xxpasixx/EvoFaderWing/docs/images/evofaderwing_keyboard_matrix_wring.png

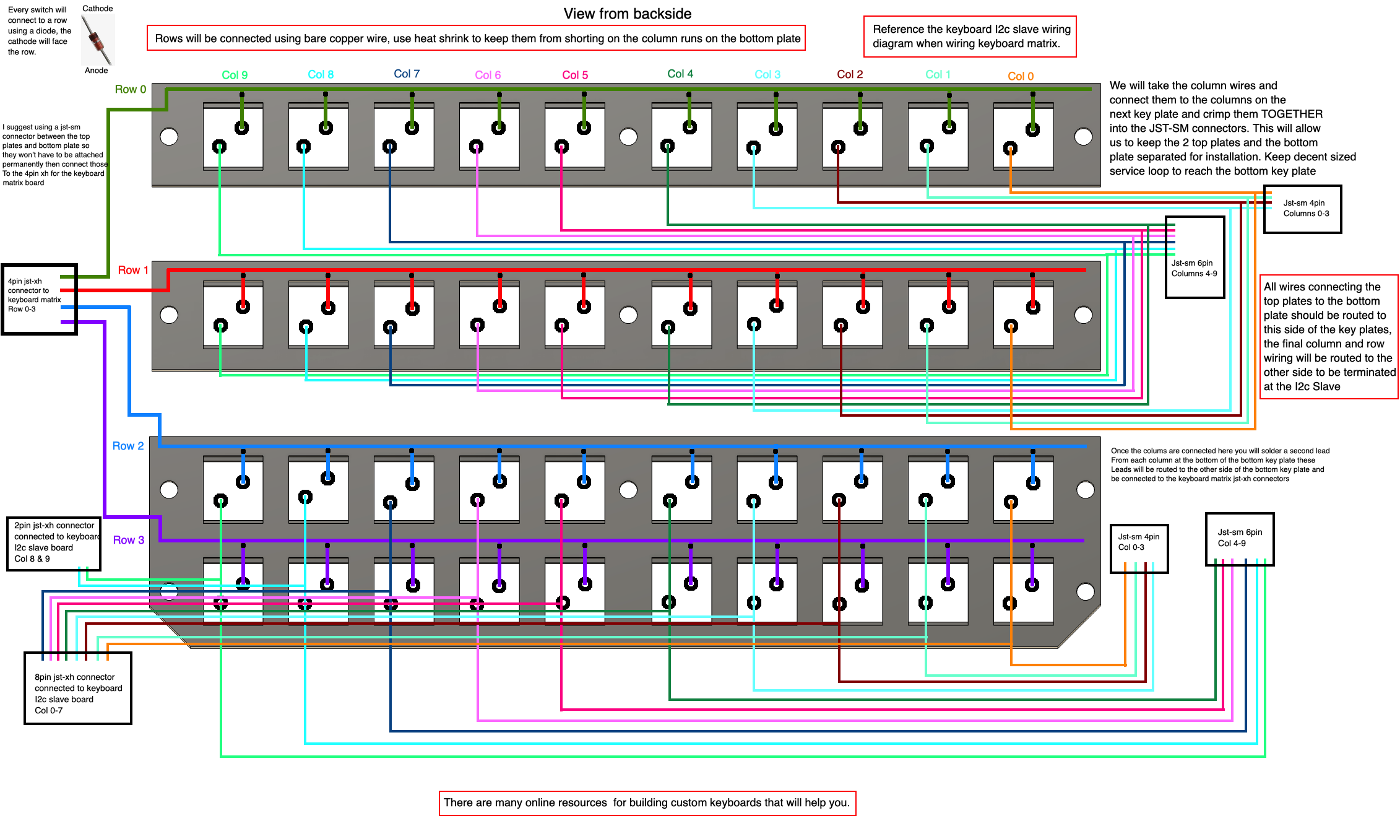
docs/images/evofaderwing_keyboard_matrix_wring.png
