xxpasixx/EvoFaderWing/docs/images/fader_images/fader_power_rail.jpeg

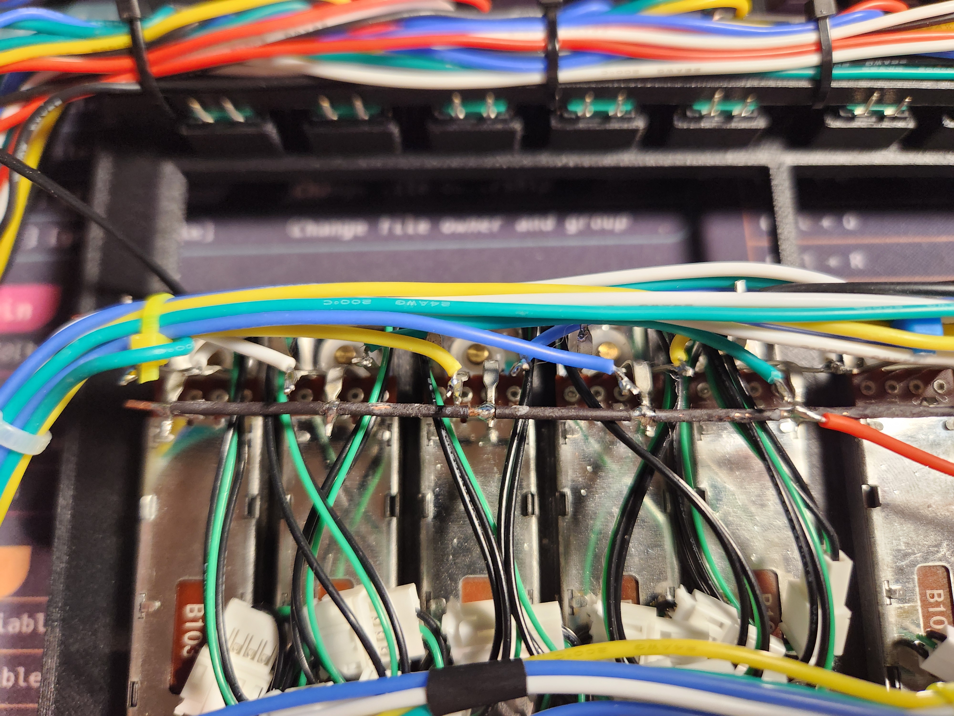
docs/images/fader_images/fader_power_rail.jpeg
