xxpasixx/EvoFaderWing/docs/images/keyplate_images/key_plates_top_middle.jpeg

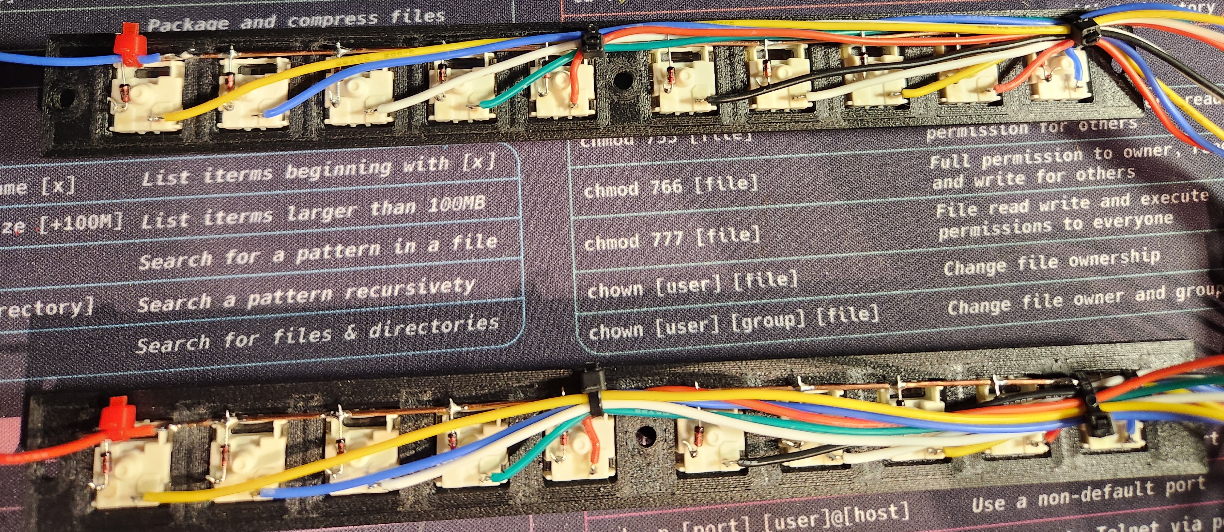
docs/images/keyplate_images/key_plates_top_middle.jpeg
