xxpasixx/EvoFaderWing/docs/images/led_images/led_connectors_tuckedin.jpg

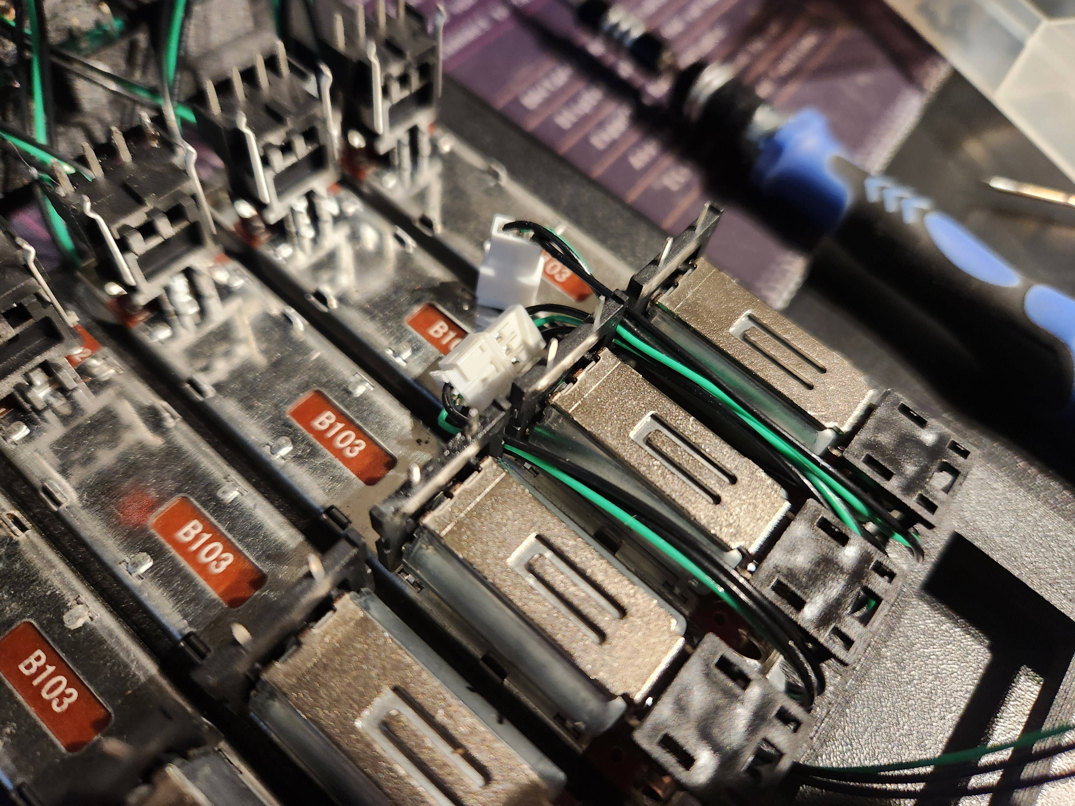
docs/images/led_images/led_connectors_tuckedin.jpg
