xxpasixx/EvoFaderWing/docs/images/led_images/led_strip_placed.jpg

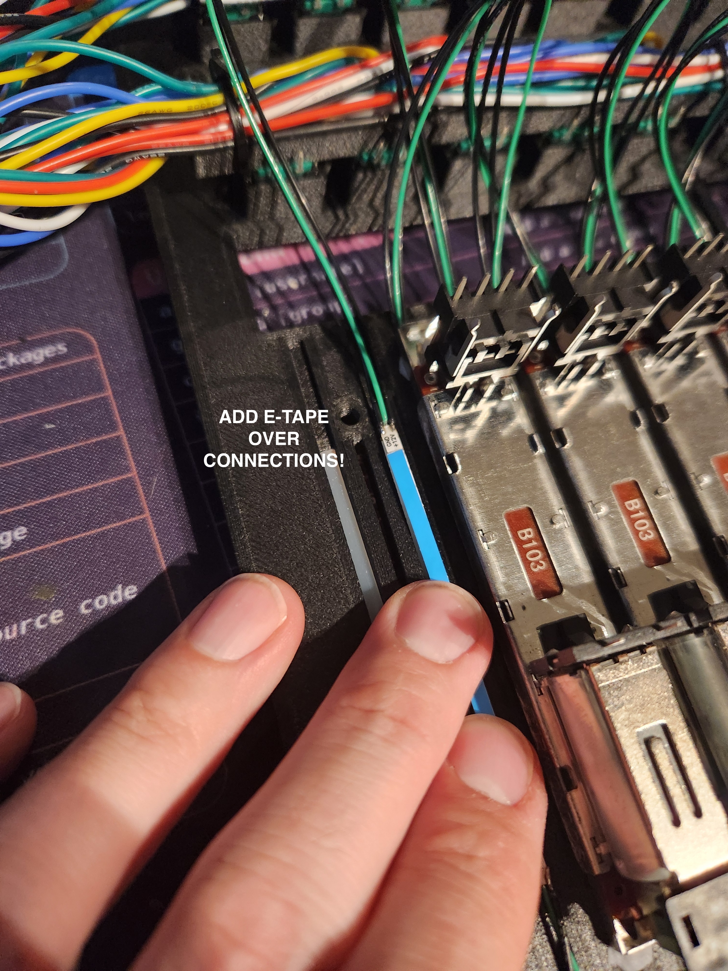
docs/images/led_images/led_strip_placed.jpg
