xxpasixx/EvoFaderWing/docs/images/misc/20250524_153631.jpg

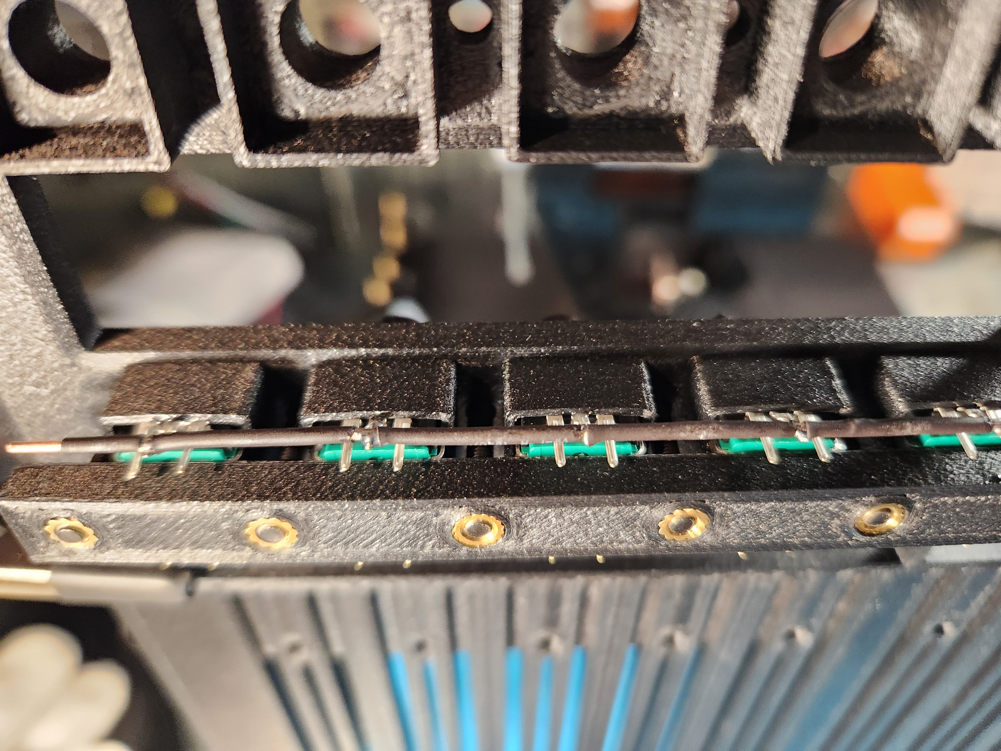
docs/images/misc/20250524_153631.jpg
