xxpasixx/EvoFaderWing/docs/images/misc/20250524_165157.jpg

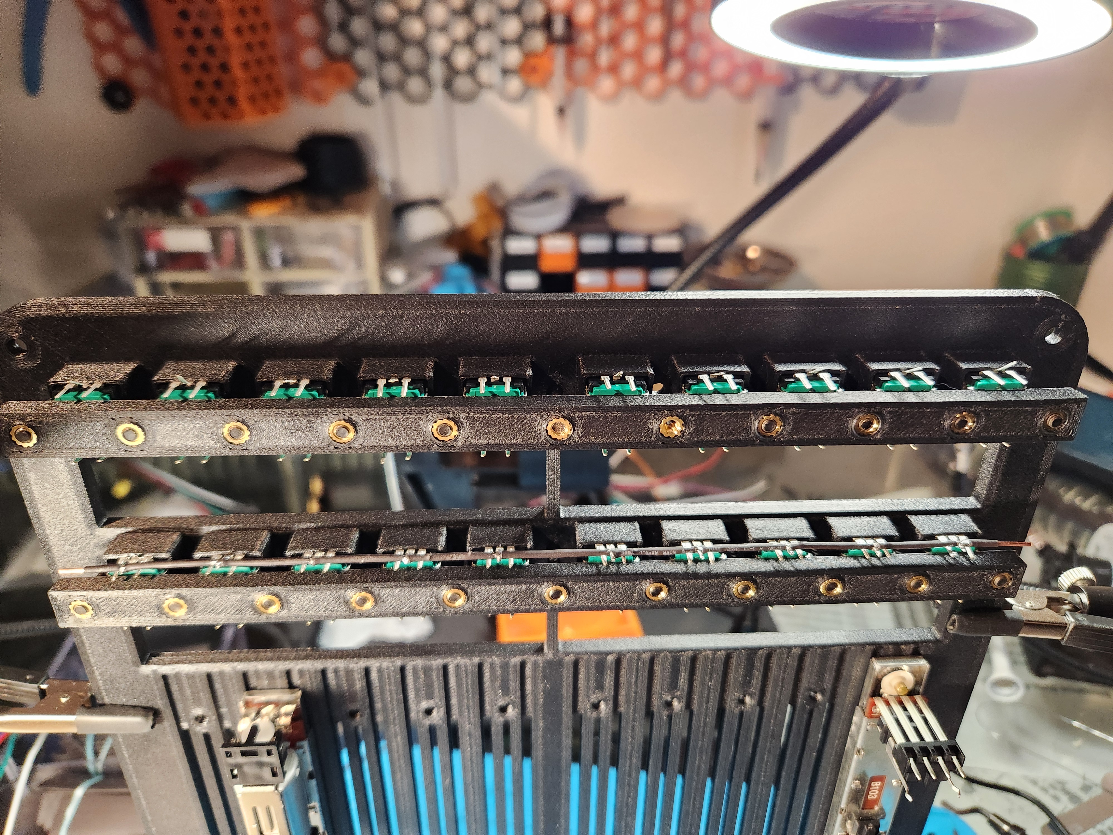
docs/images/misc/20250524_165157.jpg
