xxpasixx/EvoFaderWing/docs/images/misc/20250524_171109.jpg

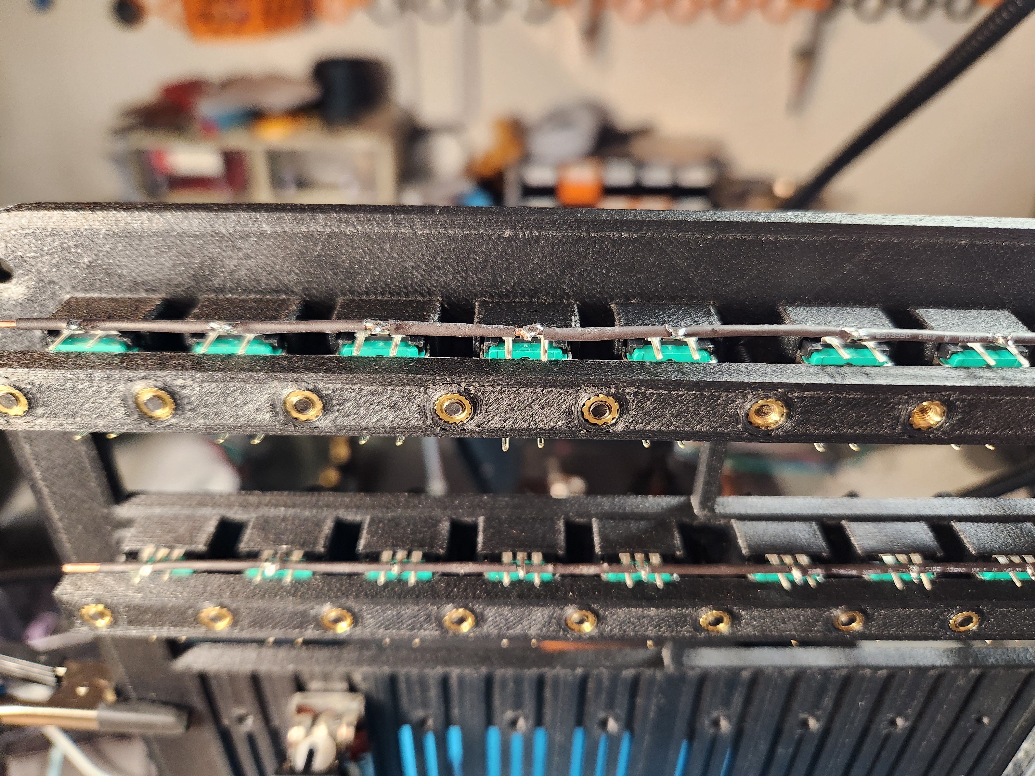
docs/images/misc/20250524_171109.jpg
