xxpasixx/EvoFaderWing/docs/images/misc/20250525_133858.jpg

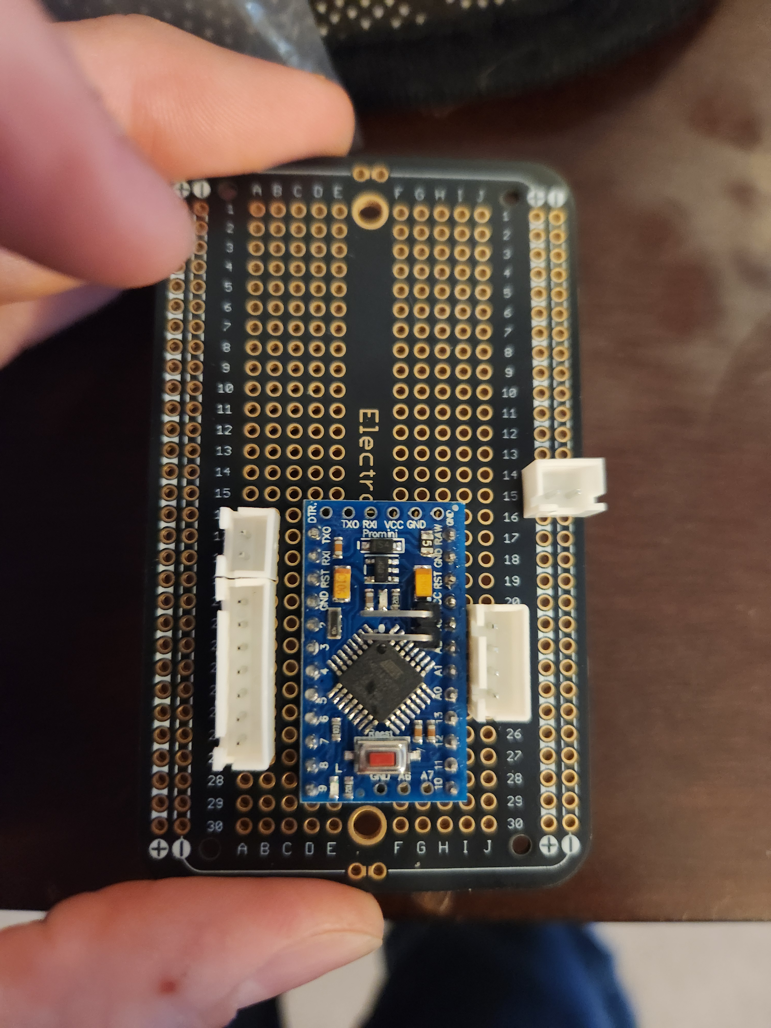
docs/images/misc/20250525_133858.jpg
