xxpasixx/EvoFaderWing/docs/images/misc/20250607_174612.jpg

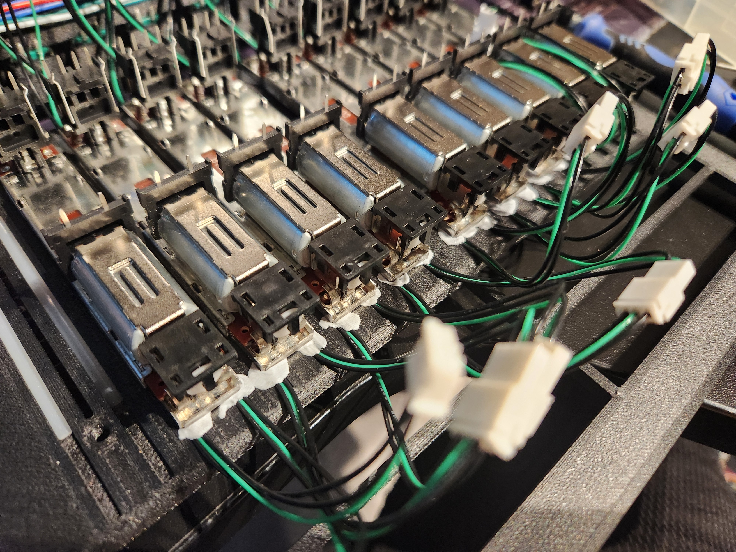
docs/images/misc/20250607_174612.jpg
