xxpasixx/EvoFaderWing/docs/images/misc/20250607_201828.jpg

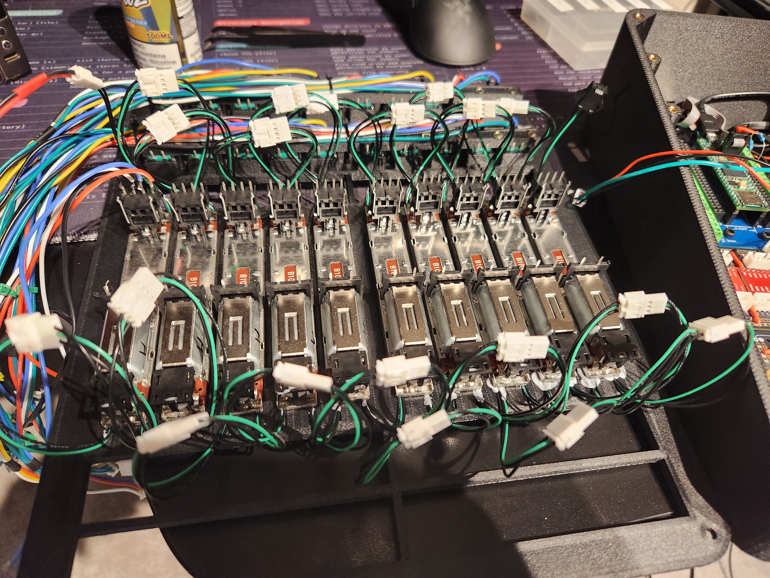
docs/images/misc/20250607_201828.jpg
