xxpasixx/EvoFaderWing/docs/images/misc/20250608_192833.jpg

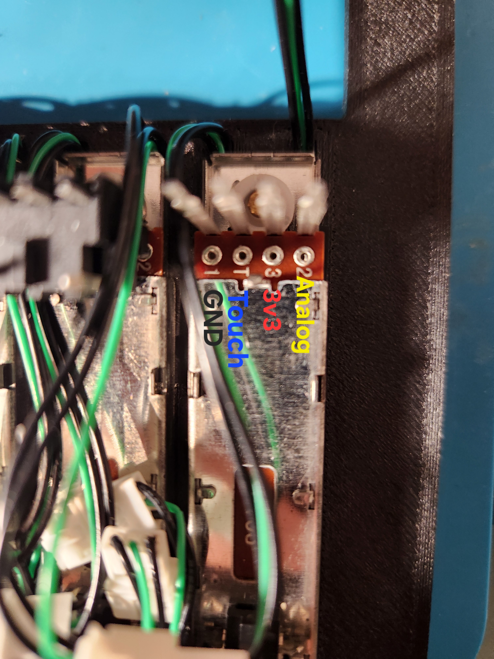
docs/images/misc/20250608_192833.jpg
