xxpasixx/EvoFaderWing/docs/images/misc/20250608_230007.jpg

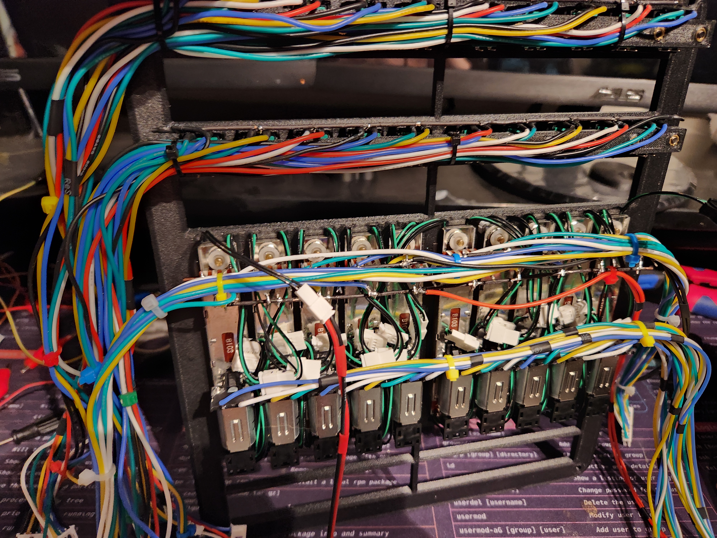
docs/images/misc/20250608_230007.jpg
