xxpasixx/EvoFaderWing/docs/images/misc/20250608_230014.jpg

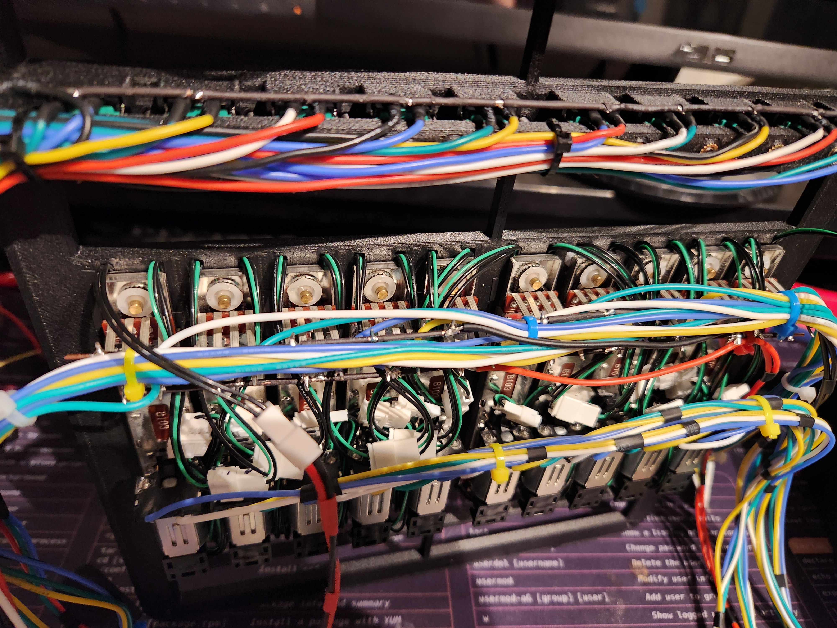
docs/images/misc/20250608_230014.jpg
