xxpasixx/EvoFaderWing/docs/images/misc/20250608_230018.jpg

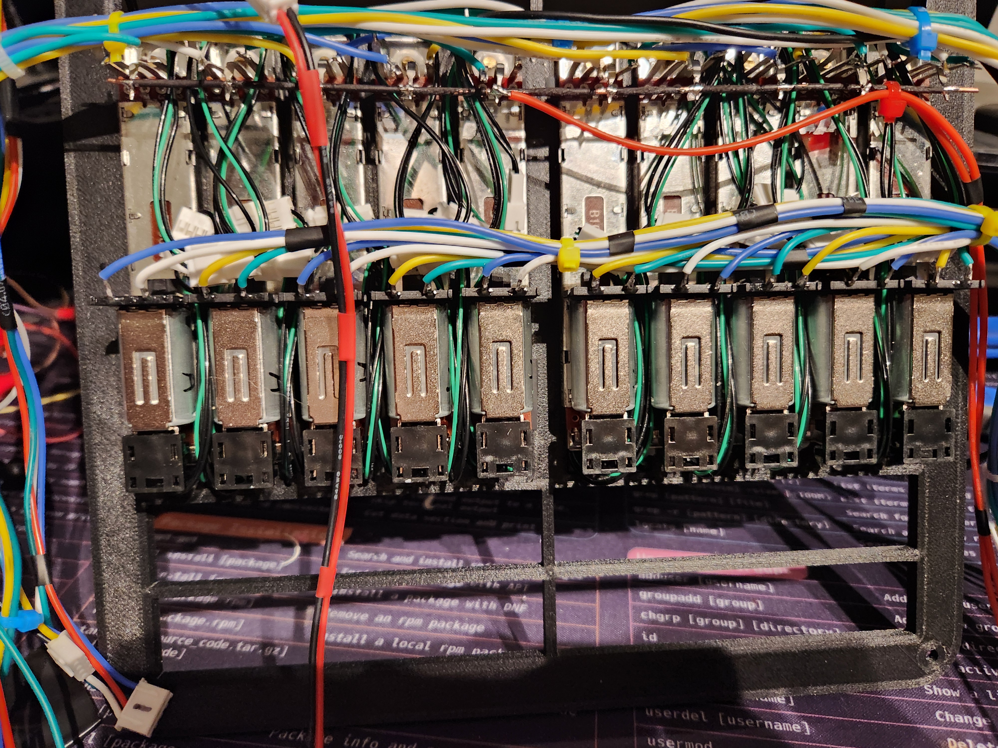
docs/images/misc/20250608_230018.jpg
