xxpasixx/EvoFaderWing/docs/images/misc/20250608_230021.jpg

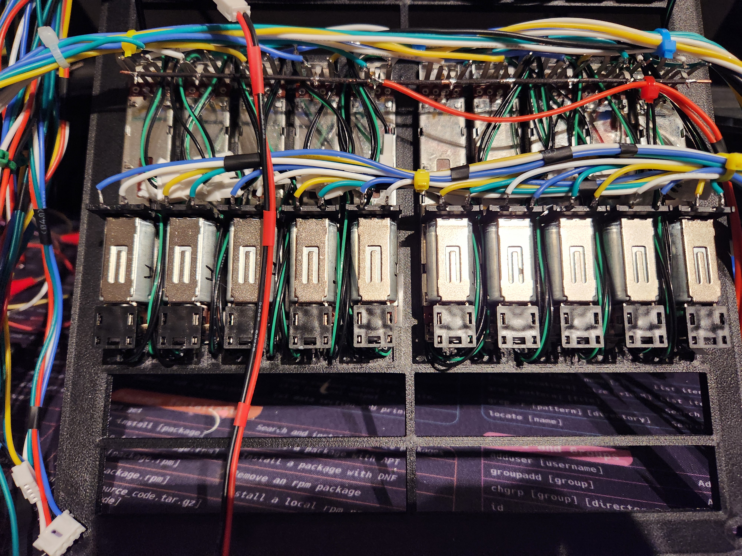
docs/images/misc/20250608_230021.jpg
