xxpasixx/EvoFaderWing/docs/images/misc/20250609_000330.jpg

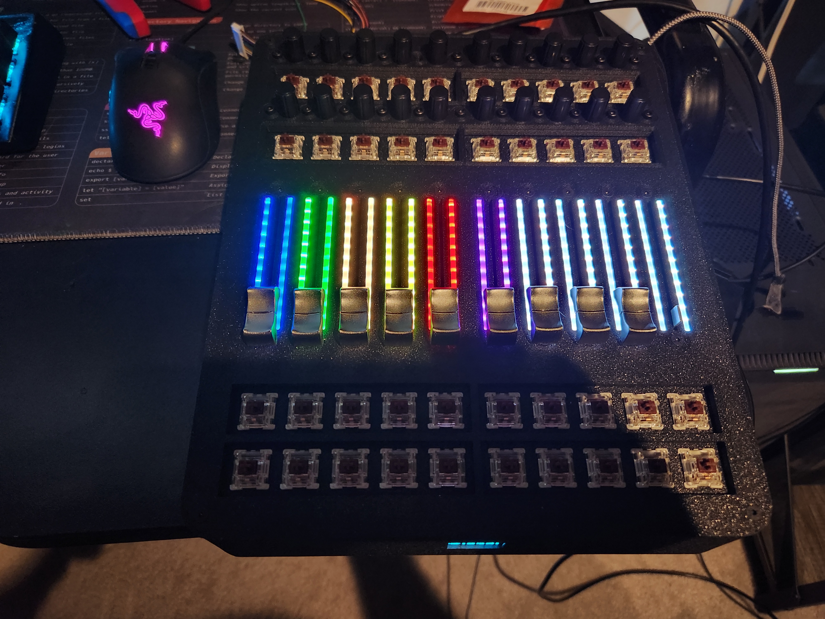
docs/images/misc/20250609_000330.jpg
