xxpasixx/EvoFaderWing/docs/images/misc/20250616_111618.jpg

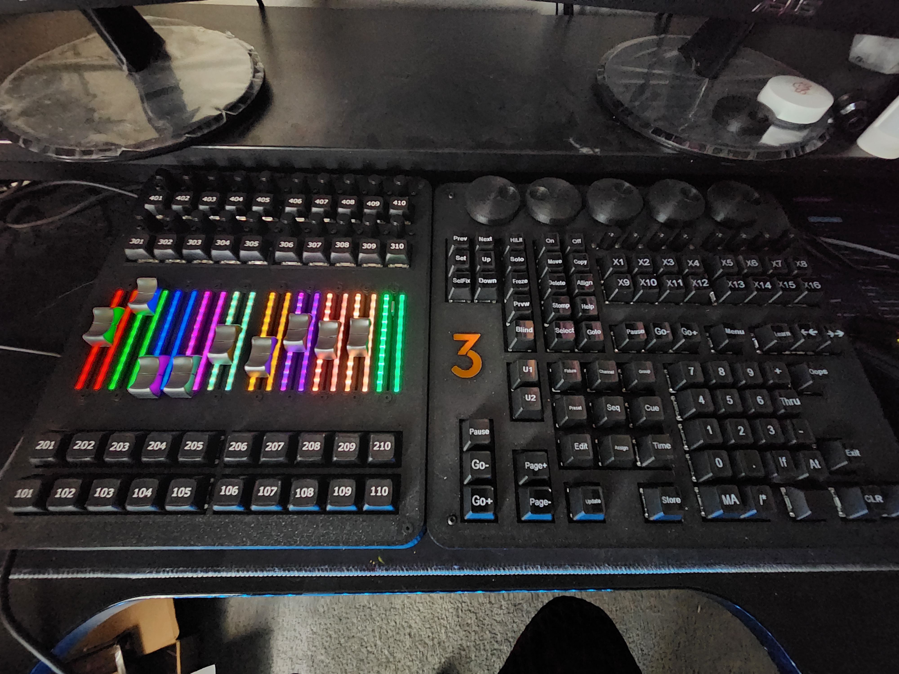
docs/images/misc/20250616_111618.jpg
