xxpasixx/EvoFaderWing/docs/images/pin_assignment.png

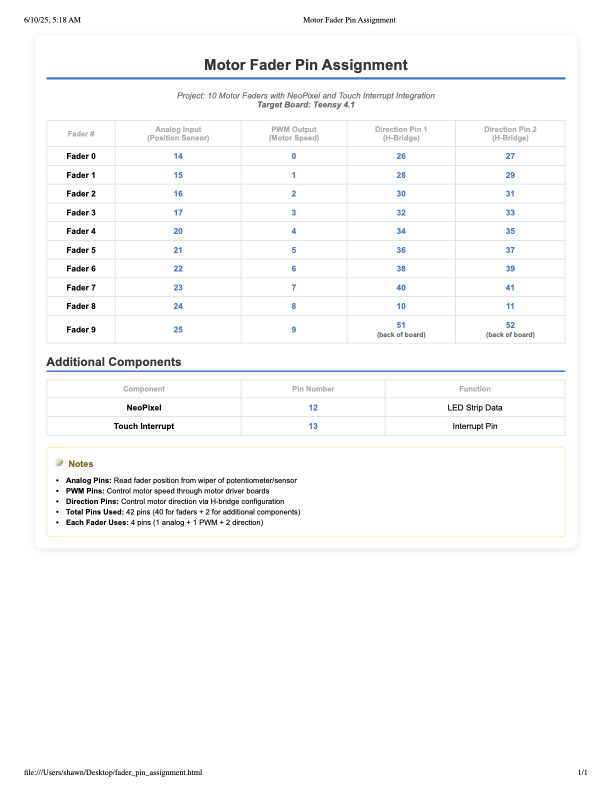
docs/images/pin_assignment.png
