xxpasixx/EvoFaderWing/docs/images/assembly/assembly_7.jpg

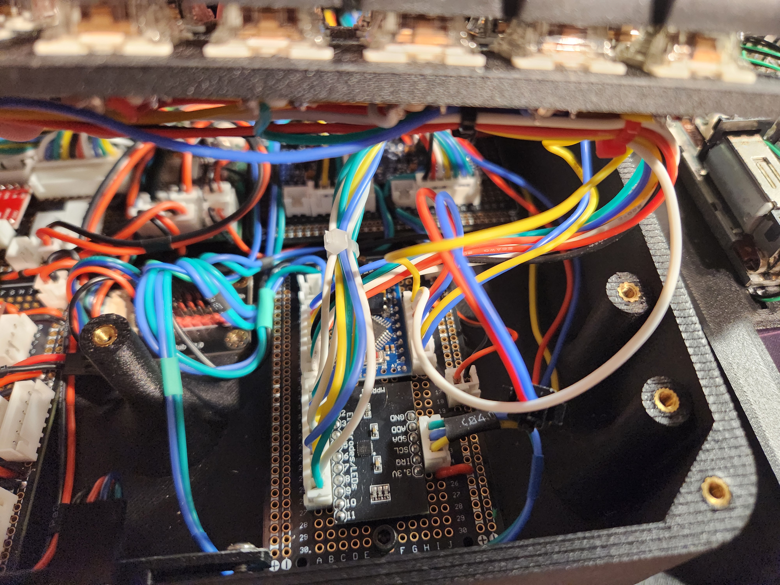
docs/images/assembly/assembly_7.jpg
