xxpasixx/EvoFaderWing/docs/images/assembly/assembly_9.jpg

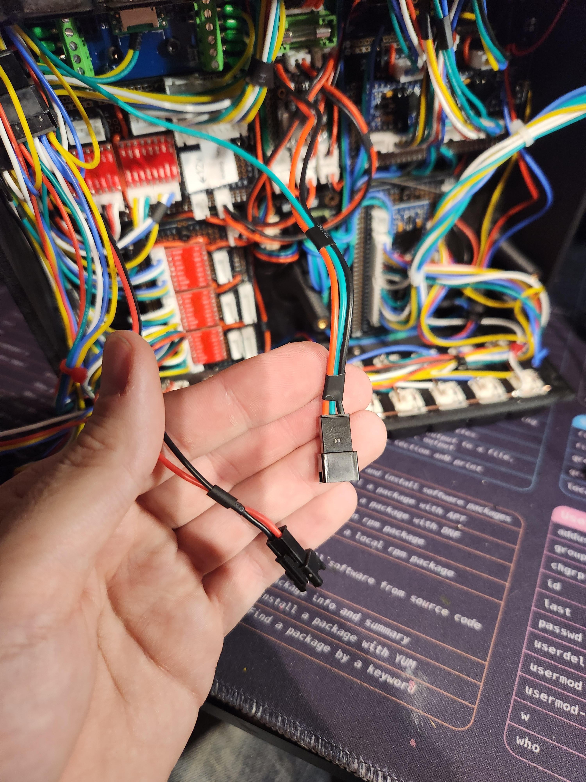
docs/images/assembly/assembly_9.jpg
