xxpasixx/EvoFaderWing/docs/images/assembly/assembly_10.jpg

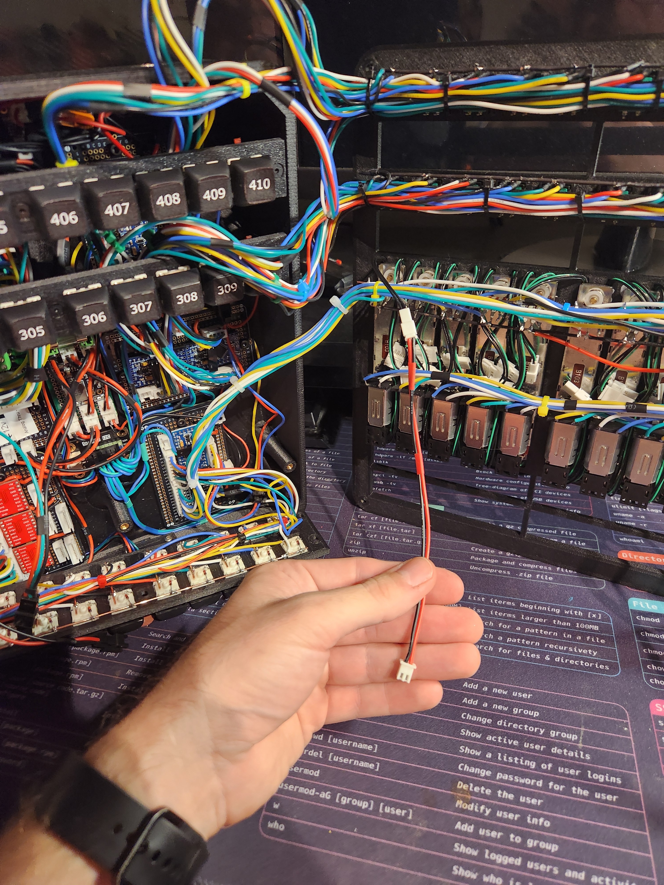
docs/images/assembly/assembly_10.jpg
