xxpasixx/EvoFaderWing/docs/images/assembly/assembly_14.jpg

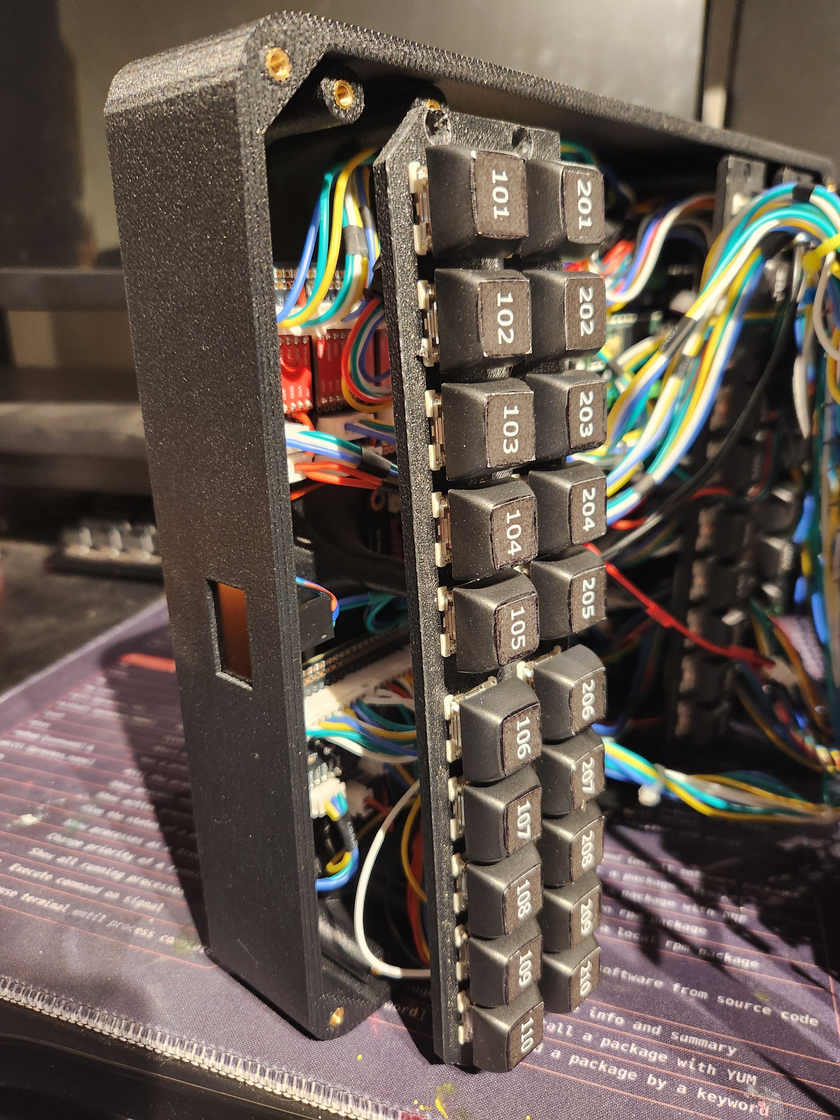
docs/images/assembly/assembly_14.jpg
