xxpasixx/EvoFaderWing/docs/images/evofaderwing_encoder_slave_wiring.png

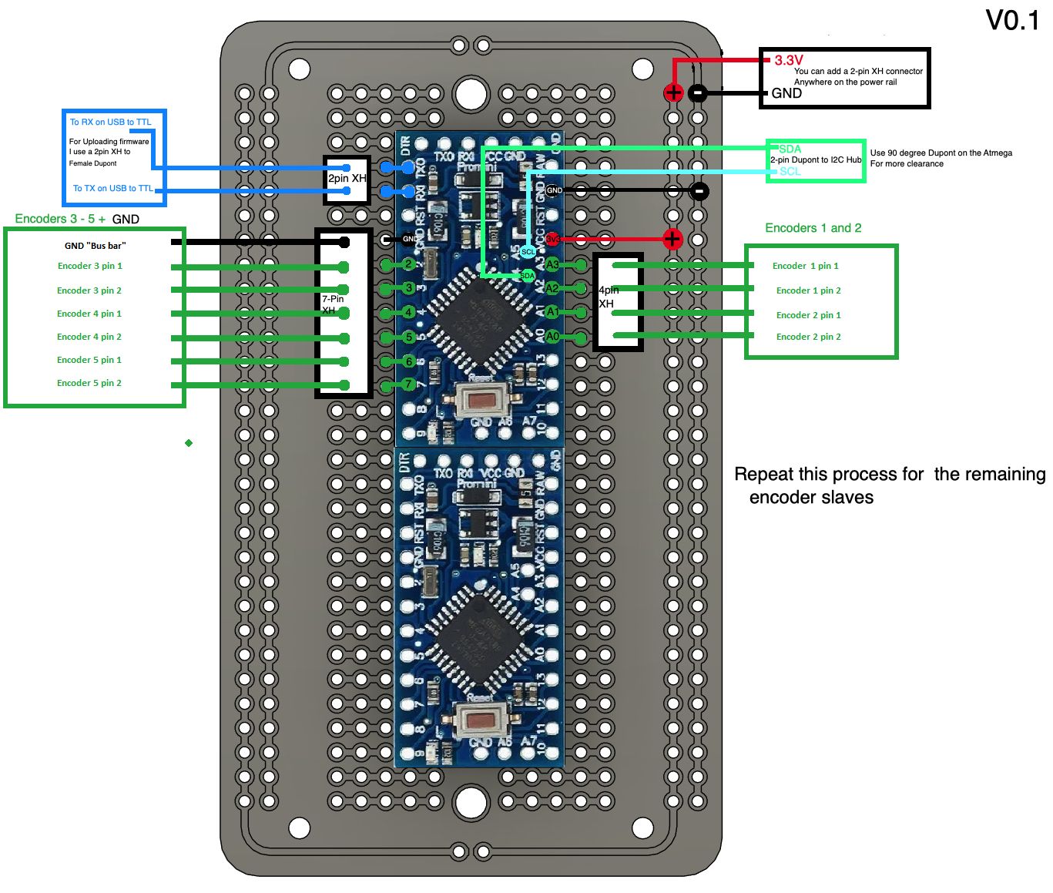
docs/images/evofaderwing_encoder_slave_wiring.png
