xxpasixx/EvoFaderWing/docs/images/evofaderwing_motor_wiring.png

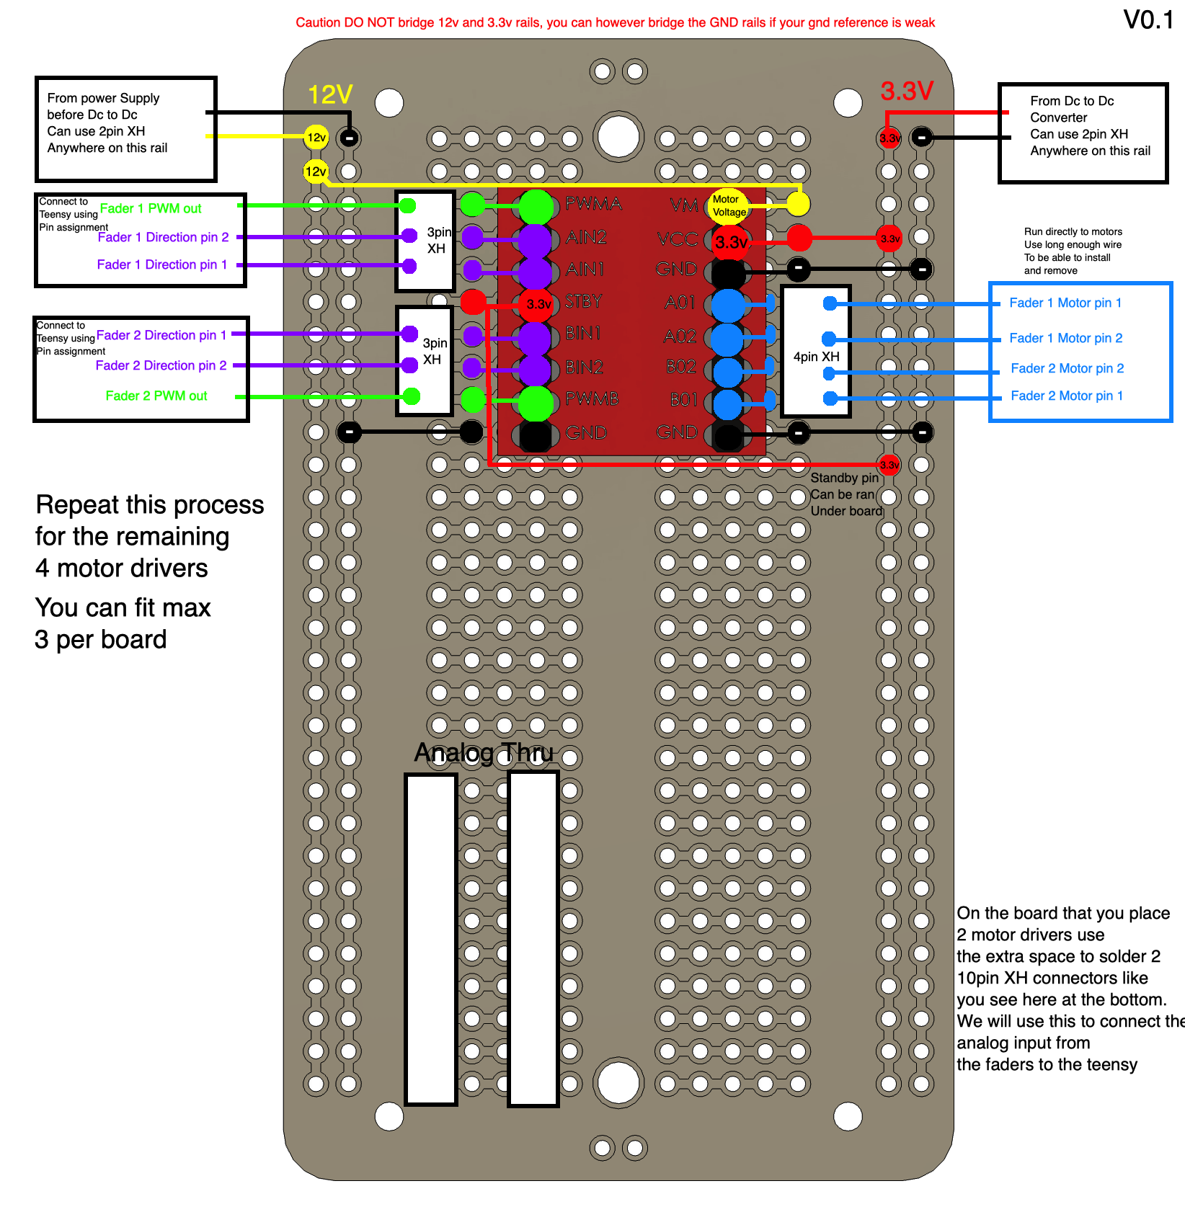
docs/images/evofaderwing_motor_wiring.png
