xxpasixx/EvoFaderWing/src/Config.cpp

// Config.cpp
#include "Config.h"

//================================
// MAIN FADER ARRAY
//================================
// Holds runtime data for each motorized fader.
// This is the primary data structure manipulated by control logic.
Fader faders[NUM_FADERS];

//================================
// PIN CONFIGURATION ARRAYS
//================================
// Analog input pins connected to fader position sensors (wipers).
const uint8_t ANALOG_PINS[NUM_FADERS] = {14, 15, 16, 17, 20, 21, 22, 23, 24, 25};

// PWM output pins used to control fader motor speed via motor drivers.
const uint8_t PWM_PINS[NUM_FADERS] = {0, 1, 2, 3, 4, 5, 6, 7, 8, 9};

//USE 12 for NEOPIXEL
//USE 41 for MRP121/MTCH2120 IRQ
//USE 18 (SDA), 19(SCL) for I2C

// Motor direction control pins — each fader has two pins for H-bridge control.
const uint8_t DIR_PINS1[NUM_FADERS] = {26, 28, 30, 32, 34, 36, 38, 40, 10, 51};
const uint8_t DIR_PINS2[NUM_FADERS] = {27, 29, 31, 33, 35, 37, 39, 41, 11, 52};

// Unique OSC IDs for each fader (used to construct OSC address strings).
const uint16_t OSC_IDS[NUM_FADERS] = {201, 202, 203, 204, 205, 206, 207, 208, 209, 210};

//================================
// FADER BEHAVIOR CONFIGURATION
//================================
// Default PID and motor tuning settings shared across all faders.
FaderConfig Fconfig = {
  .minPwm = MIN_PWM,
  .maxPwm = MAX_PWM,
  .calibratePwm = CALIB_PWM,
  .targetTolerance = TARGET_TOLERANCE,
  .sendTolerance = SEND_TOLERANCE,
  .slowZone = SLOW_ZONE,
  .fastZone = FAST_ZONE,
  .baseBrightness = 5,
  .touchedBrightness = 40,
  .fadeTime = 500,
  .serialDebug = debugMode,
  .sendKeystrokes = false,
  .useLevelPixels = false

};

// Executor LED defaults
ExecConfig execConfig = {
  .baseBrightness = EXECUTOR_BASE_BRIGHTNESS,
  .activeBrightness = EXECUTOR_ACTIVE_BRIGHTNESS,
  .useStaticColor = false,
  .staticRed = 255,
  .staticGreen = 255,
  .staticBlue = 255,
  .reserved = {0, 0}
};

//================================
// NETWORK CONFIGURATION
//================================
// Default static network settings and UDP destination info.
// These values can be updated at runtime or overridden via web UI.
NetworkConfig netConfig = {
  IPAddress(192, 168, 0, 169),     // staticIP
  IPAddress(192, 168, 0, 1),       // gateway
  IPAddress(255, 255, 255, 0),     // subnet
  IPAddress(192, 168, 0, 10),     // sendToIP (OSC target)
  8000,                            // receivePort (OSC listening)
  9000,                            // sendPort (OSC destination)
  true                             // useDHCP (fallback to static if false)
};

// Network reset check
bool checkForReset = true;
unsigned long resetCheckStartTime = 0;

// Calibration state flag
bool calibrationInProgress = false;


//================================
// DEBUG SETTINGS
//================================
#ifdef DEBUG
  bool debugMode = true;  // Enables or disables verbose serial output
#else
  bool debugMode = false;  // Enables or disables verbose serial output
#endif

//================================
// TOUCH SENSOR GLOBALS
//================================
// These are used by the touch driver and web UI configuration.
int autoCalibrationMode = 1;      // 0 = AutoTune off, 1 = AutoTune on
#if defined(TOUCH_SENSOR_MTCH2120)
uint8_t touchThreshold = 128;     // Higher = less sensitive (MTCH2120 per-key threshold)
uint8_t releaseThreshold = 1;     // Hysteresis code 0-7
#else
uint8_t touchThreshold = 12;      // Higher = less sensitive (MPR121 default)
uint8_t releaseThreshold = 6;     // Lower = harder to release (MPR121 default)
#endif


// Page Tracking
int currentOSCPage = 1;  // Default to page 1
