xxpasixx/EvoFaderWing/include/Utils.h

// Utils.h
#ifndef UTILS_H
#define UTILS_H

#include <Arduino.h>
#include <IPAddress.h>

//================================
// DEBUG FUNCTIONS
//================================

// Debug print functions - only output if debug mode is enabled
void debugPrint(const char* message);
void debugPrintf(const char* format, ...);


//================================
// UPLOAD FUNCTION
//================================
void checkSerialForReboot();   //Allow us to upload without pressing physical button
void processSerialCommand(String cmd);

//================================
// IP ADDRESS UTILITIES
//================================

// IP address conversion helpers
String ipToString(IPAddress ip);
IPAddress stringToIP(const String &str);

//================================
// WEB PARAMETER PARSING
//================================

// Extract parameter from URL query string
String getParam(String data, const char* key);

// Reset Teensy
void resetTeensy();

#endif // UTILS_H
