xxpasixx/EvoFaderWing/docs/images/led_images/led_strips.jpg

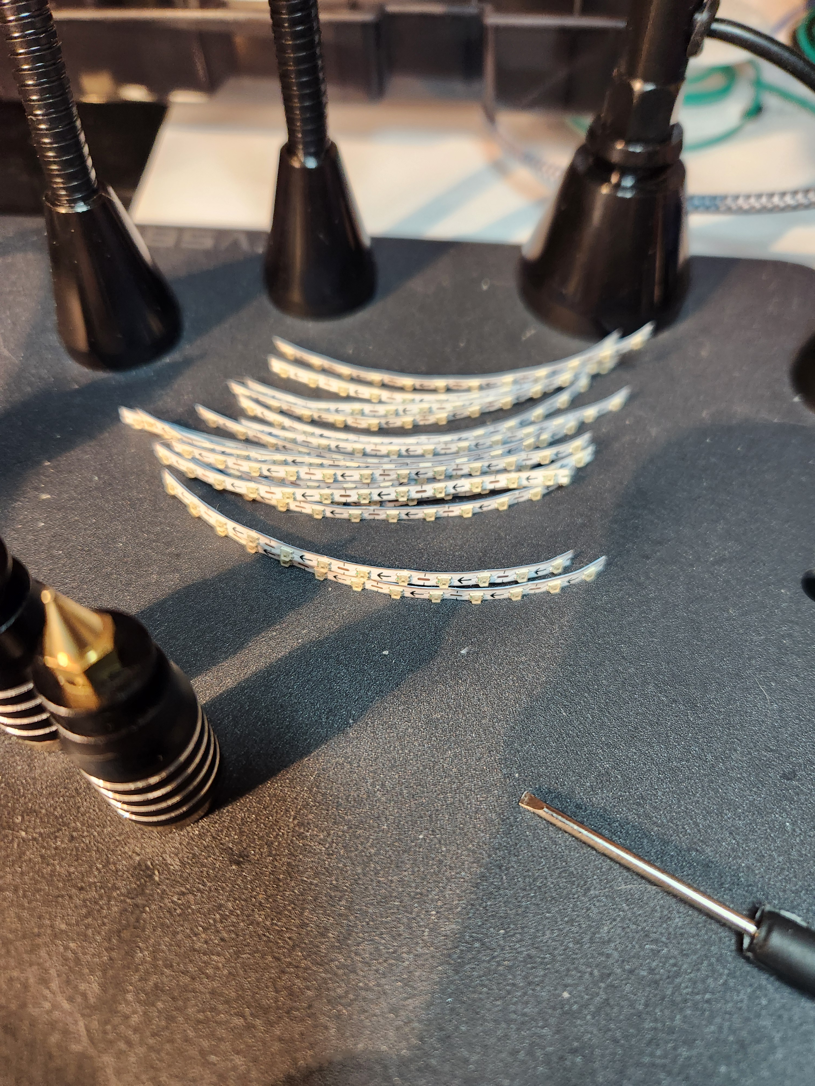
docs/images/led_images/led_strips.jpg
