xxpasixx/EvoFaderWing/docs/images/misc/20250525_185512.jpg

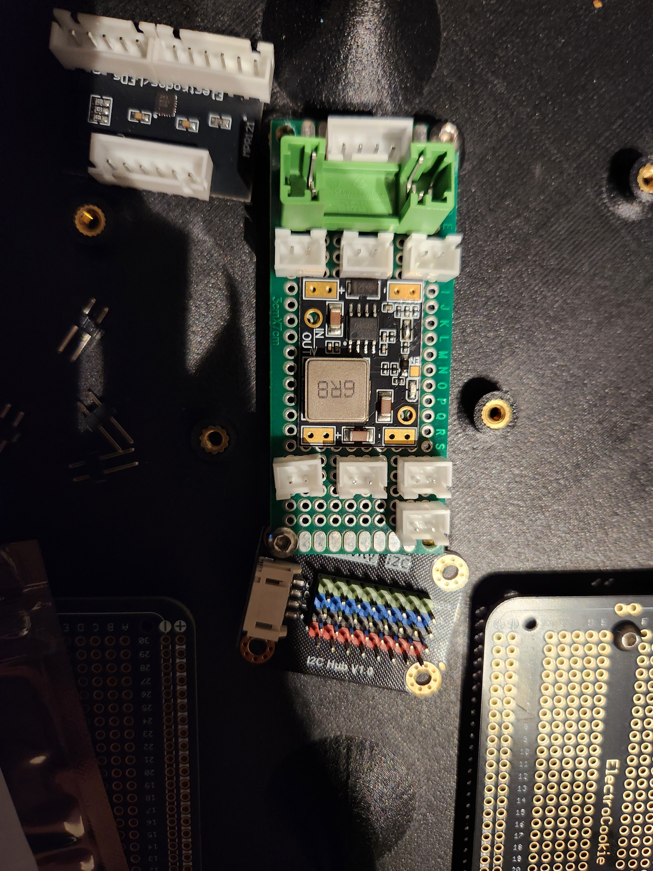
docs/images/misc/20250525_185512.jpg
