xxpasixx/EvoFaderWing/docs/images/misc/20250530_231826.jpg

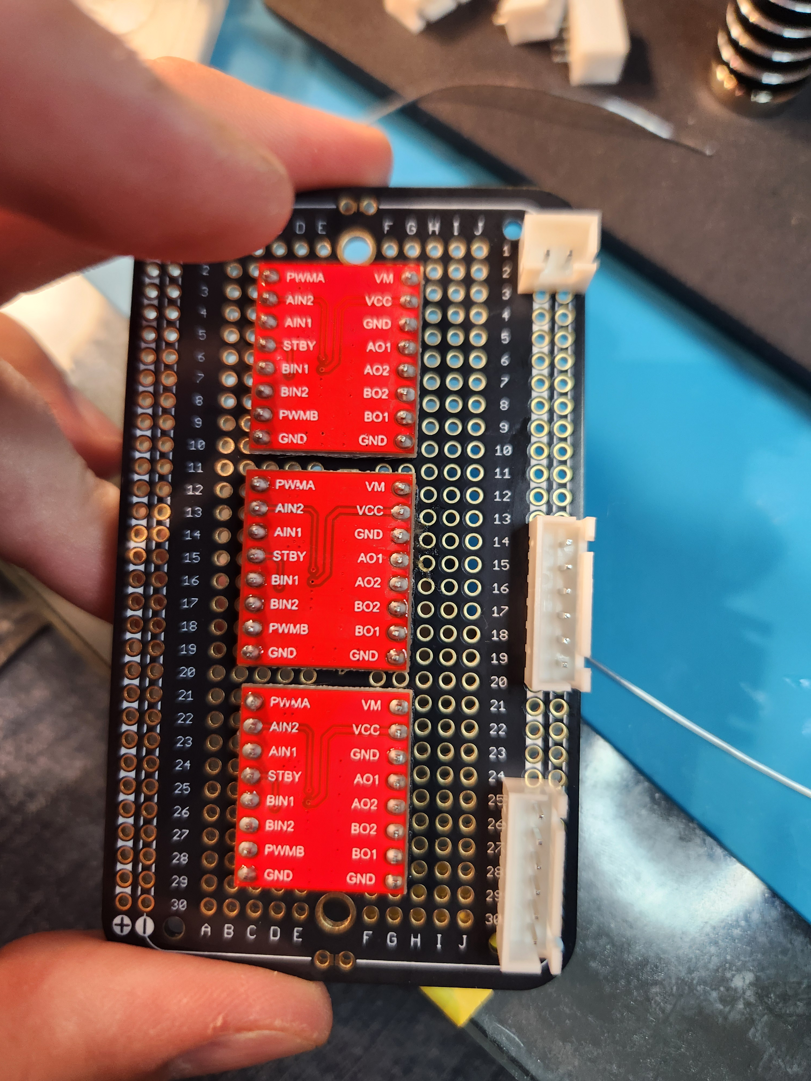
docs/images/misc/20250530_231826.jpg
