xxpasixx/EvoFaderWing/docs/images/misc/20250607_174801.jpg

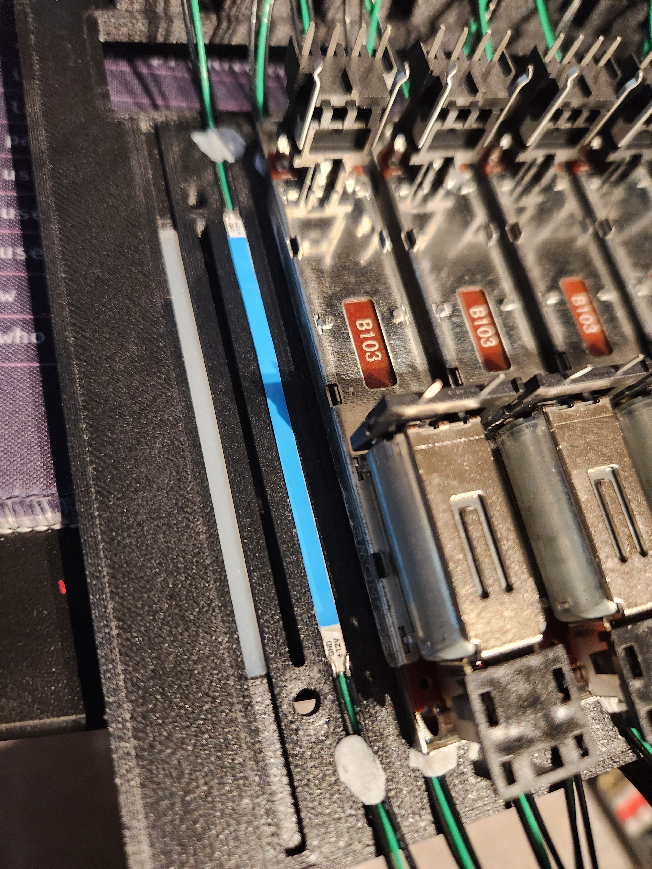
docs/images/misc/20250607_174801.jpg
