xxpasixx/EvoFaderWing/docs/images/misc/20250607_175227.jpg

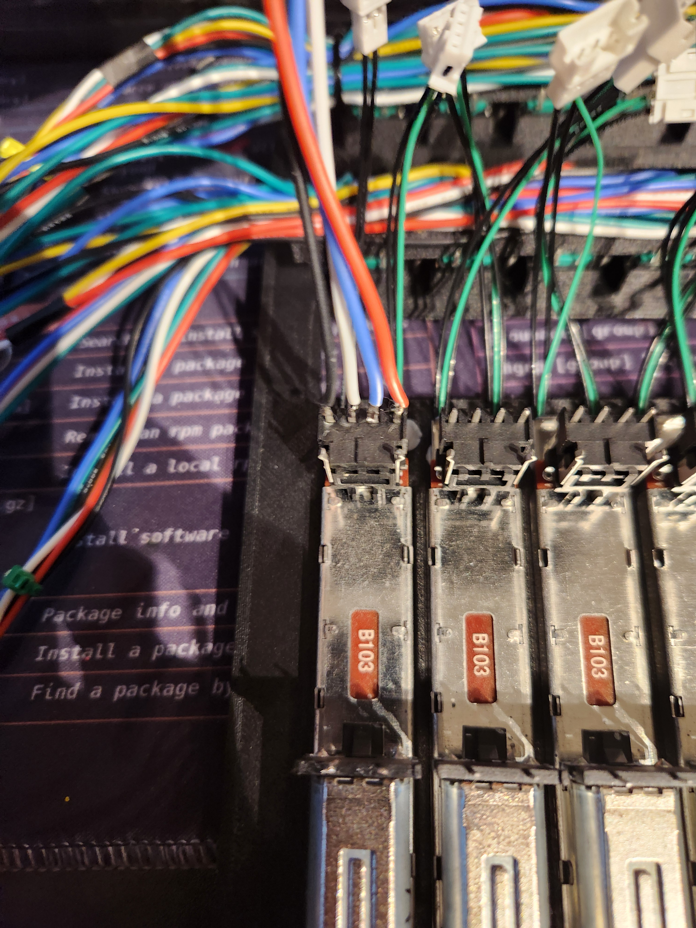
docs/images/misc/20250607_175227.jpg
