xxpasixx/EvoFaderWing/docs/images/misc/20250607_201822.jpg

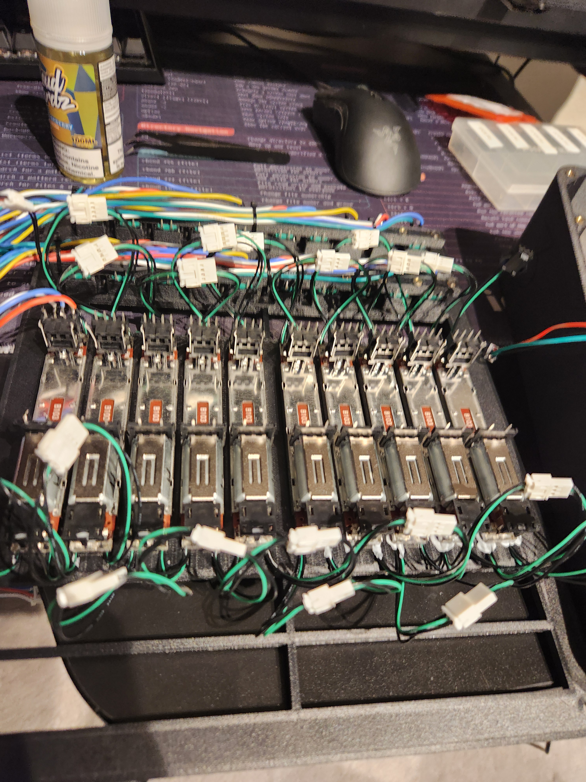
docs/images/misc/20250607_201822.jpg
