xxpasixx/EvoFaderWing/docs/images/misc/20250608_225934.jpg

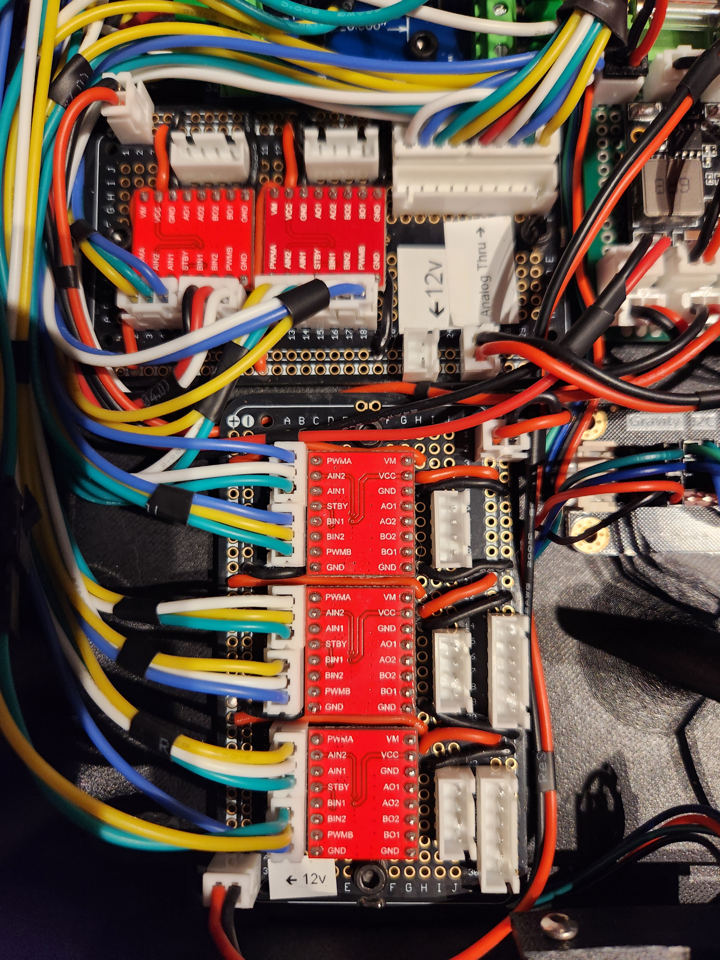
docs/images/misc/20250608_225934.jpg
