xxpasixx/EvoFaderWing/docs/images/misc/20250608_225937.jpg

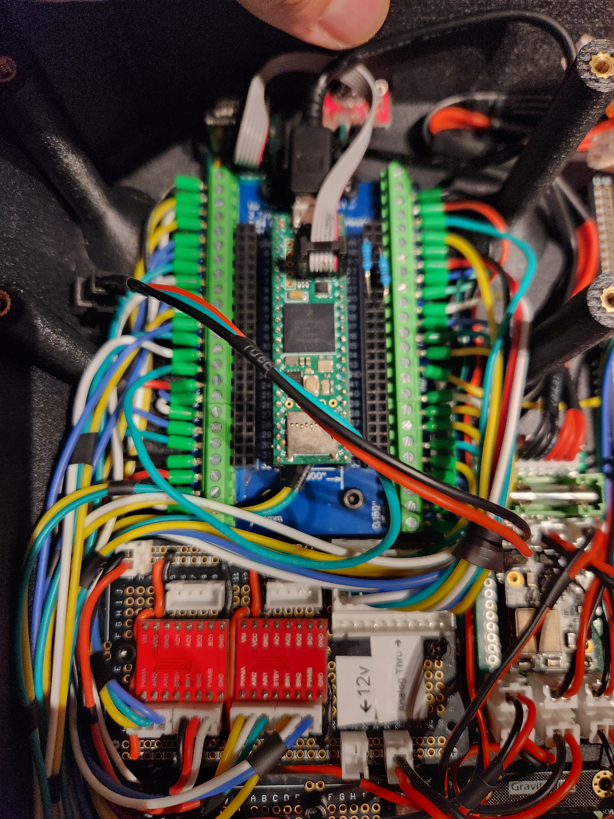
docs/images/misc/20250608_225937.jpg
