xxpasixx/EvoFaderWing/docs/images/misc/20250608_225939.jpg

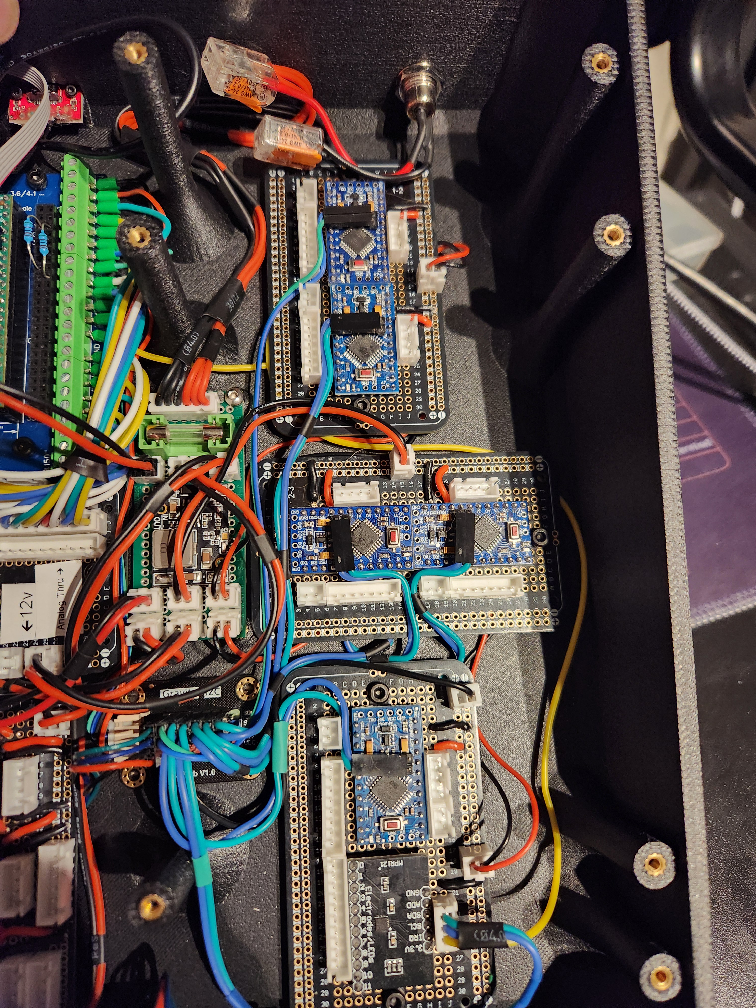
docs/images/misc/20250608_225939.jpg
