xxpasixx/EvoFaderWing/docs/images/misc/20250608_225953.jpg

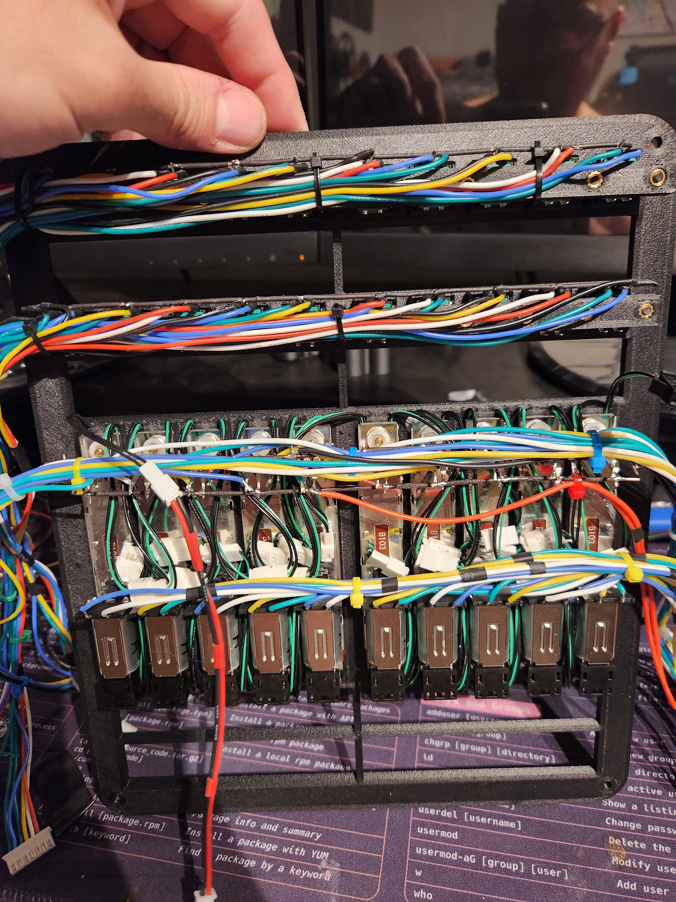
docs/images/misc/20250608_225953.jpg
