xxpasixx/EvoFaderWing/docs/images/misc/20250608_230002.jpg

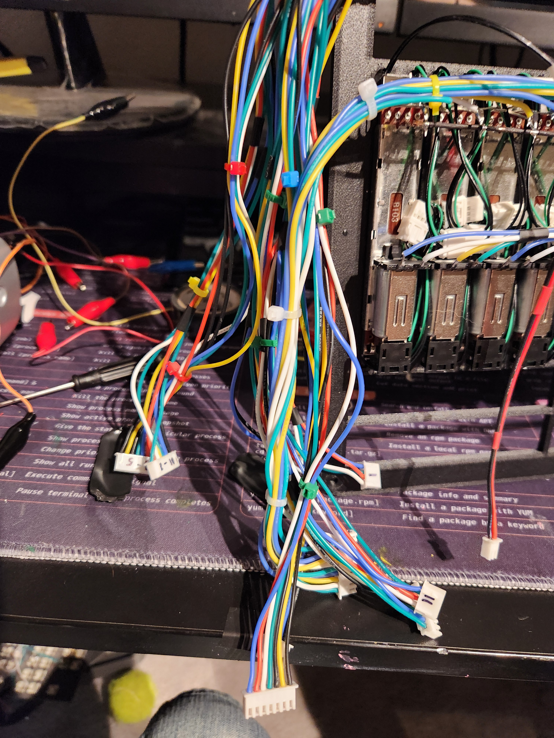
docs/images/misc/20250608_230002.jpg
